gcolbourn/Prusa3-SemiU/box_frame/x-end_zippy_SemiU.scad

// PRUSA iteration3
// X ends
// GNU GPL v3
// Josef Průša <josefprusa@me.com>
// Václav 'ax' Hůla <axtheb@gmail.com>
// http://www.reprap.org/wiki/Prusa_Mendel
// http://github.com/prusajr/PrusaMendel

include <configuration.scad>
use <bushing.scad>
use <inc/bearing-guide.scad>
use <inc/bearing_new.scad>
use <y-drivetrain.scad>

//height and width of the x blocks depend on x smooth rod radius
x_box_height = 52 + 2 * bushing_xy[0];
x_box_width = (bushing_xy[0] <= 4) ? 17.5 : bushing_xy[0] * 2 + 9.5;
echo(x_box_width);
bearing_height = max ((bushing_z[2] > 30 ? x_box_height : (2 * bushing_z[2] + 8)), x_box_height);

module x_end_motor(){

    mirror([0, 1, 0]) {

        x_end_base([3, 3, min((bushing_xy[0] - 3) * 2, 3), 2], len=42, offset=-5, thru=false);

//z endstop adjuster
            rotate([0,0,180]){
            translate([19.7, 14, x_box_height-5]) {               
                difference(){
			cube_fillet([23, 10, 10], center = true, vertical=[8, 0, 0, 5]);
              translate([7, -1, 0]) rotate([0, 0, 0]){
                //m3 bolt
                translate([0, 0, -10]) cylinder(h=(4.1 / 2 + 35), r=1.35, $fn=32);
                //m3 nut
//                translate([0, 0, -1]) cylinder(r=2.9, h=9.1, center = true, $fn=6);
//               translate([0, 0, 2]) cylinder(r=2.9, h=9.1, center = true, $fn=6);
        translate([11, 0, -2]) rotate([0,50,0]) cube([15, 20, 40], center=true);

					}
				}
           		 }
}

        translate([0, -z_delta - 2, 0]) difference(){
            union(){
                intersection() {
                    translate([-15, -34, 30]) cube([20, 60, x_box_height], center = true);
                    union() {
                        translate([-14, -16 + z_delta / 2, 24]) cube_fillet([17.5, 10.5 + z_delta, 55], center = true, vertical=[0, 0, 3, 3], top=[0, 3, 6, 3], $fn=16);
                        //lower arm holding outer stepper screw
                        translate([-10.25, -34, 9]) intersection(){
                            translate([0, 0, -5]) cube_fillet([10, 37, 28], center = true, vertical=[0, 0, 0, 0], top=[0, 3, 5, 3]);
                            translate([-10/2, 10, -26]) rotate([45, 0, 0]) cube_fillet([10, 60, 60], radius=2);
                        }
                    }
                }
                translate([-16, -32, 30.25]) rotate([90, 0, 0])  rotate([0, 90, 0]) nema17(places=[1, 0, 1, 1], h=11);
            }

            // motor screw holes
            translate([21-5, -21-11, 30.25]){
                // belt hole
                    translate([-30, 11, -0.25]) cube_fillet([11, 36, 22], vertical=0, top=[0, 1, 0, 1], bottom=[0, 1, 0, 1], center = true, $fn=4);
                //motor mounting holes
                translate([-29.5, 0, 0]) rotate([0, 0, 0])  rotate([0, 90, 0]) nema17(places=[1, 1, 0, 1], holes=true, shadow=5.5, $fn=small_hole_segments, h=8);
            }
        }
        //smooth rod caps
        //translate([-22, -10, 0]) cube([17, 2, 15]);
        //translate([-22, -10, 45]) cube([17, 2, 10]);
    }
}

module x_end_base(vfillet=[3, 3, 3, 3], thru=true, len=40, offset=0){
v = [-14,0, 29];

    difference()
{
        union(){
            translate([-10 - bushing_xy[0], -10 + len / 2 + offset, 30]) cube_fillet([x_box_width, len, x_box_height], center=true, vertical=vfillet, top=[5, 3, 5, 3]);

            translate([0, 0, 4 - bushing_xy[0]]) {
                //rotate([0, 0, 0]) translate([0, -9.5, 0]) 
                //translate([z_delta, 0, 0]) %linear(bushing_z, bearing_height);
				translate(v) rotate([90,0,90]) horizontal_bearing_base_bis(2);
		
                // Nut trap
                translate([-2, 18, 5]) cube_fillet([20, 14, 10], center = true, vertical=[8, 0, 0, 5]);
                //}
            }
        }
        // here are bushings/bearings
        //translate([z_delta, 0, 4 - bushing_xy[0]]) linear_negative(bushing_z, bearing_height);
		translate(v) rotate([90,0,90]) horizontal_bearing_holes(2);

        // belt hole
        translate([-5.5 - 10 + 1.5, 22 - 9 + offset, 30]) cube_fillet([max(idler_width + 2, 11), 55, 27], center = true, vertical=0, top=[0, 1, 0, 1], bottom=[0, 1, 0, 1], $fn=4);

        //smooth rods
//        translate([-10 - bushing_xy[0], offset, 0]) {
        translate([-10 - bushing_xy[0], offset-5, 0]) {
            if(thru == true){
                translate([0, -11, 6]) rotate([-90, 0, 0]) pushfit_rod(bushing_xy[0] * 2 + 0.2, 100);
                translate([0, -11, xaxis_rod_distance+6]) rotate([-90, 0, 0]) pushfit_rod(bushing_xy[0] * 2 + 0.2, 100);
            } else {
                translate([0, -7, 6]) rotate([-90, 0, 0]) pushfit_rod(bushing_xy[0] * 2 + 0.2, 50);
                translate([0, -7, xaxis_rod_distance+6]) rotate([-90, 0, 0]) pushfit_rod(bushing_xy[0] * 2 + 0.2, 50);
            }
        }
        translate([0, 0, 5 - bushing_xy[0]]) {  // m5 nut insert
            translate([0, 17, 0]) rotate([0, 0, 10]){
                //rod
                translate([0, 0, -1]) cylinder(h=(4.1 / 2 + 5), r=3, $fn=32);
                //nut
                translate([0, 0, 9]) cylinder(r=4.6, h=14.1, center = true, $fn=6);

            }
        }
    }
    //threaded rod
    translate([0, 17, 0]) %cylinder(h = 70, r=2.5+0.2);
}

module x_end_idler(){

boxwidth=3;squaresides=15;
bearings=2;
 one_holder_lenght = 8+25;
 holder_lenght = 8+bearings*25;
a=[90,0,0];
difference(){union(){
translate([-22.75, -30 - z_delta / 2, 30+squaresides/2]) {
            rotate([0, 90, 0]) cube([squaresides,squaresides+5,boxwidth]);};
translate([-22.75, -30 - z_delta / 2, 30+squaresides/2]) {
            rotate([0, 90, 0])  rotate([0, 0, 45]) cube([squaresides,squaresides,boxwidth]);}
translate([-22.75, -30 - z_delta / 2 + squaresides/sqrt(2), 30+(squaresides/2)-4.5]) {
            rotate([0, 90, 0])  rotate([0, 0, -45]) cube([squaresides,squaresides,boxwidth]);};

translate([-8.25, -30 - z_delta / 2, 30+squaresides/2]) {
            rotate([0, 90, 0]) cube([squaresides,squaresides+5,boxwidth]);};
translate([-8.25, -30 - z_delta / 2, 30+squaresides/2]) {
            rotate([0, 90, 0])  rotate([0, 0, 45]) cube([squaresides,squaresides,boxwidth]);}
translate([-8.25, -30 - z_delta / 2 + squaresides/sqrt(2), 30+(squaresides/2)-4.5]) {
            rotate([0, 90, 0])  rotate([0, 0, -45]) cube([squaresides,squaresides,boxwidth]);};};

translate([-40, -25 - z_delta / 2, 30]) {
       rotate([0, 90, 0]) cylinder(r=m4_diameter / 2, h=100, center=true, $fn=small_hole_segments);};
translate([-40, -25 - z_delta / 2, 30 + m4_diameter / 2]) {
            rotate([0, 90, 0]) cube([m4_diameter,11,35]);};
translate([-40, -14 - z_delta / 2, 30]) {
       rotate([0, 90, 0]) cylinder(r=m4_diameter / 2, h=100, center=true, $fn=small_hole_segments);};

 // Ziptie cutouts
// ziptie_cut_ofset = 0;
translate([-1.5,12,29]) rotate([90,0,0]){
 for ( i = [0 : bearings-1] ){
  // For easier positioning I move them by half of one 
  // bearing holder then add each bearign lenght and then center again
  translate(v=[0,-holder_lenght/2,0]) translate(v=[0,one_holder_lenght/2+i*25,0]) 
difference(){
   union(){
    translate(v=[0,2-6,12]) rotate(a)  cylinder(h = 4, r=12.5, $fn=50);
    translate(v=[0,2+6,12]) rotate(a)  cylinder(h = 4, r=12.5, $fn=50);
   }
   translate(v=[0,10,12]) rotate(a)  cylinder(h = 24, r=10, $fn=50);
 
 }
}
}


};



    difference() {
        x_end_base(len=48 + z_delta / 3, offset=-10 - z_delta / 3);
        // idler hole
        translate([-20, -15 - z_delta / 2, 30]) {
            rotate([0, 90, 0]) cylinder(r=m4_diameter / 2, h=33, center=true, $fn=small_hole_segments);
//            translate([15 - 2 * single_wall_width, 0, 0]) rotate([90, 0, 90]) cylinder(r=m4_nut_diameter_horizontal / 2, h=3, $fn=6);
    }
translate([-40, -27 - z_delta / 2, 30 + m4_diameter / 2]) {
            rotate([0, 90, 0]) cube([m4_diameter,15,35]);}



        translate([-6 - x_box_width, 11, 29.5 - (max(idler_bearing[0], 16) / 2)]) cube([x_box_width + 1, 11, 1.5 + max(idler_bearing[0], 16)]);
    }
        %translate([-14, -9, 30.5 - (max(idler_bearing[0], 16) / 2)]) x_tensioner();


}

//module x_tensioner(len=62, idler_height=max(idler_bearing[0], 16)) {
//        idlermount(len=len, rod=m4_diameter / 2, idler_height=idler_height, narrow_len=46, narro//w_width=idler_width + 2 - single_wall_width);
//}


//translate([-40, 0, 4 - bushing_xy[0]]) x_tensioner();
translate([0, -80, 0]) mirror([1, 0, 0]) x_end_idler(thru=true);
translate([-50, 0, 0]) mirror([1, 0, 0]) translate([-50, 0, 0])
    x_end_motor();

module pushfit_rod(diameter, length){
    cylinder(h = length, r=diameter/2, $fn=30);
    translate([0, -diameter/4, length/2]) cube_fillet([diameter, diameter/2, length], vertical = [0, 0, 1, 1], center = true, $fn=4);

    translate([0, -diameter/2-1.2, length/2]) cube([diameter - 1, 1, length], center = true);
}


//render() x_end_base();

//if (idler_bearing[3] == 1) {
//    translate([-33,  -33 - idler_bearing[0] / 2, 0]) {
//        render() bearing_guide_inner();
//        translate([0, -(idler_bearing[0]+10), 0])
//            render()bearing_guide_outer();
//    }
//}
